jerry20091103/OpenMacro/OpenMacro-GUI/App/mainwindow.h

#ifndef MAINWINDOW_H
#define MAINWINDOW_H

#include <QMainWindow>
#include "./presetdialog.h"

QT_BEGIN_NAMESPACE
namespace Ui { class MainWindow; }
QT_END_NAMESPACE

class MainWindow : public QMainWindow
{
    Q_OBJECT

public:
    MainWindow(QWidget *parent = nullptr);
    ~MainWindow();
private:
    Ui::MainWindow *ui;
    PresetDialog *presetDialog;
private slots:
    void Test();
};
#endif // MAINWINDOW_H
