jerry20091103/OpenMacro/OpenMacro-GUI/App/debugmenu.cpp

#include "debugmenu.h"

const char* debugPortName = "COM19";

DebugMenu::DebugMenu(QWidget* parent) : QMenu(parent)
{

}

static QSerialPort* initSerialPort(){
    auto serialPort = new QSerialPort();
    auto openMode = QIODeviceBase::OpenMode();
    openMode.setFlag(QIODeviceBase::OpenModeFlag::ReadWrite);

    serialPort->setPortName(debugPortName);

    serialPort->open(openMode);

    serialPort->setBaudRate(QSerialPort::Baud9600);
    serialPort->setDataBits(QSerialPort::Data8);
    serialPort->setParity(QSerialPort::NoParity);
    serialPort->setStopBits(QSerialPort::OneStop);
    serialPort->setFlowControl(QSerialPort::NoFlowControl);
    return serialPort;
}

void DebugMenu::testSerial(void (*testFunc)(QSerialPort*)){
    QSerialPort* serialPort = initSerialPort();
    testFunc(serialPort);
    serialPort->close();
    delete serialPort;
}

void DebugMenu::testSerialRead(QSerialPort* serialPort){
    qDebug() << "TestSerialRead";
    if(serialPort->isOpen()){
        while (!serialPort->canReadLine())
                serialPort->waitForReadyRead(-1);
        auto readResult = serialPort->readLine ();
        qDebug() << readResult;
    }
    else qDebug() << "Failed to open port" << debugPortName;
}

void DebugMenu::testSerialWrite(QSerialPort* serialPort){
    qDebug() << "TestSerialWrite";
    if(serialPort->isOpen() && serialPort->isWritable()){
        int bytesWritten = serialPort->write("Hello from Qt");
        serialPort->flush();
        if(bytesWritten == -1) qDebug() << "Failed to write bytes to" << debugPortName;
        else qDebug() << "Wrote " << bytesWritten << " to" << debugPortName;
    }
    else qDebug() << "Failed to open port" << debugPortName;
}

void DebugMenu::onTestSerialWrite(){
    testSerial(testSerialWrite);
}

void DebugMenu::onTestSerialRead(){
    testSerial(testSerialRead);
}
